elabree/hub75_esp32s3/Hardware_ZeDMD/ZeDMD_ESP32-S3/ZeDMD_ESP32-S3.kicad_sch

## KiCad design Hardware_ZeDMD/ZeDMD_ESP32-S3/ZeDMD_ESP32-S3.kicad_sch (2025-09-04)

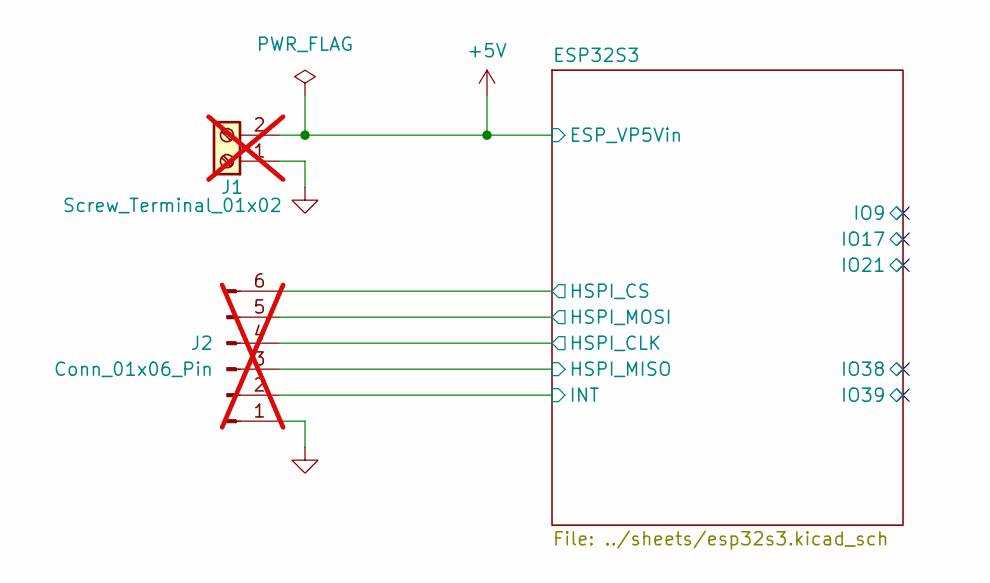
[picture p7: schematic ZeDMD_ESP32-S3.kicad_sch]

Parts:
J1: Screw_Terminal_01x02; TerminalBlock_Phoenix_MKDS-1,5-2-5.08_1x02_P5.08mm_Horizont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; not fitted
J2: Conn_01x06_Pin; PinHeader_1x06_P2.54mm_Vertical; not fitted

Connections:
+5V: J1.2
GND: J1.1, J2.1
HSPI_CLK: J2.4
HSPI_CS: J2.6
HSPI_MISO: J2.3
HSPI_MOSI: J2.5
INT: J2.2
