elabree/hub75_esp32s3/Hardware_ZeDMD/sheets/esp32s3.kicad_sch

## KiCad design Hardware_ZeDMD/sheets/esp32s3.kicad_sch (2025-09-04)

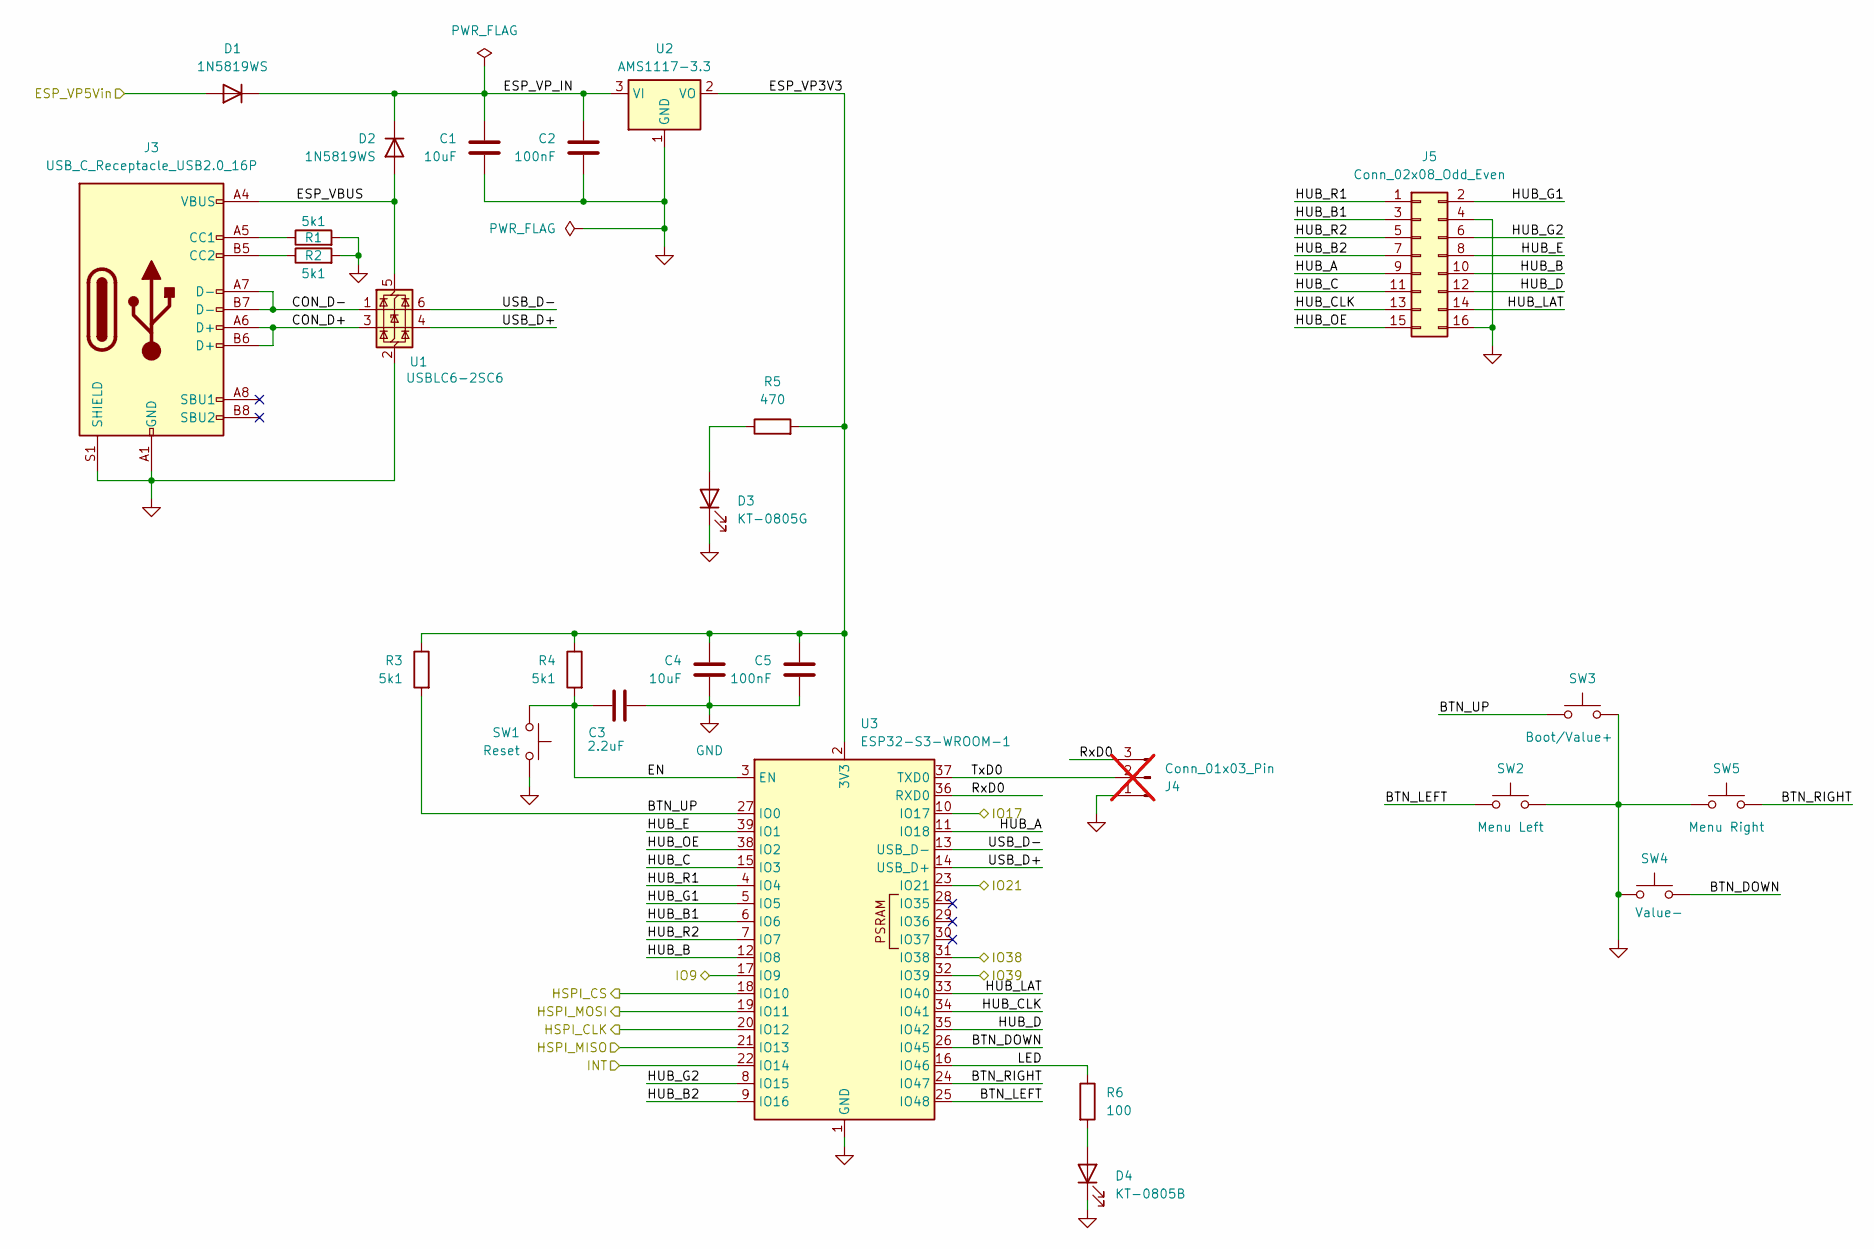
[picture p8: schematic esp32s3.kicad_sch]

Parts:
C1, C4: 10uF; C_0805_2012Metric; LCSC C15850
C2, C5: 100nF; C_0402_1005Metric; LCSC C1525
C3: 2.2uF; C_0603_1608Metric; LCSC C23630
D1, D2: 1N5819WS; D_SOD-323; LCSC C191023
D3: KT-0805G; LED_0805_2012Metric; LCSC C2297
D4: KT-0805B; LED_0805_2012Metric; LCSC C2293
J3: USB_C_Receptacle_USB2.0_16P; USB_C_Receptacle_XKB_U262-16XN-4BVC11; LCSC C709357
J4: Conn_01x03_Pin; PinHeader_1x03_P2.54mm_Vertical; not fitted
J5: Conn_02x08_Odd_Even; IDC-Header_2x08_P2.54mm_Vertical_SMD; LCSC C601969
R1, R2, R3, R4: 5k1; R_0603_1608Metric; LCSC C23186
R5: 470; R_0603_1608Metric; LCSC C23179
R6: 100; R_0603_1608Metric; LCSC C22775
SW1: Reset; SW_SPST_SKQG_WithStem; LCSC C318884
SW2: Menu Left; SW_SPST_SKQG_WithStem; LCSC C318884
SW3: Boot/Value+; SW_SPST_SKQG_WithStem; LCSC C318884
SW4: Value-; SW_SPST_SKQG_WithStem; LCSC C318884
SW5: Menu Right; SW_SPST_SKQG_WithStem; LCSC C318884
U1: USBLC6-2SC6; SOT-23-6; LCSC C7519
U2: AMS1117-3.3; SOT-223-3_TabPin2; LCSC C5346136
U3: ESP32-S3-WROOM-1; LCSC C2913202

Connections:
BTN_DOWN: SW4.1, U3.26 (IO45)
BTN_LEFT: SW2.1, U3.25 (IO48)
BTN_RIGHT: SW5.1, U3.24 (IO47)
BTN_UP: R3.2, SW3.1, U3.27 (IO0)
CON_D+: J3.A6 (D+), J3.B6 (D+), U1.3 (I/O2)
CON_D-: J3.A7 (D-), J3.B7 (D-), U1.1 (I/O1)
EN: C3.2, R4.2, SW1.2, U3.3 (EN)
ESP_VBUS: D2.2 (A), J3.A4 (VBUS), J3.A9 (VBUS), J3.B4 (VBUS), J3.B9 (VBUS), U1.5 (VBUS)
ESP_VP3V3: C4.1, C5.1, R3.1, R4.1, R5.2, U2.2 (VO), U3.2 (3V3)
ESP_VP5Vin: D1.2 (A)
ESP_VP_IN: C1.1, C2.1, D1.1 (K), D2.1 (K), U2.3 (VI)
GND: C1.2, C2.2, C3.1, C4.2, C5.2, D3.1 (K), D4.1 (K), J3.A1 (GND), J3.A12 (GND), J3.B1 (GND), J3.B12 (GND), J3.S1 (SHIELD), J4.1, J5.4, J5.16, R1.2, R2.2, SW1.1, SW2.2, SW3.2, SW4.2, SW5.2, U1.2 (GND), U2.1 (GND), U3.1 (GND), U3.40 (GND), U3.41 (GND)
HSPI_CLK: U3.20 (IO12)
HSPI_CS: U3.18 (IO10)
HSPI_MISO: U3.21 (IO13)
HSPI_MOSI: U3.19 (IO11)
HUB_A: J5.9, U3.11 (IO18)
HUB_B: J5.10, U3.12 (IO8)
HUB_B1: J5.3, U3.6 (IO6)
HUB_B2: J5.7, U3.9 (IO16)
HUB_C: J5.11, U3.15 (IO3)
HUB_CLK: J5.13, U3.34 (IO41)
HUB_D: J5.12, U3.35 (IO42)
HUB_E: J5.8, U3.39 (IO1)
HUB_G1: J5.2, U3.5 (IO5)
HUB_G2: J5.6, U3.8 (IO15)
HUB_LAT: J5.14, U3.33 (IO40)
HUB_OE: J5.15, U3.38 (IO2)
HUB_R1: J5.1, U3.4 (IO4)
HUB_R2: J5.5, U3.7 (IO7)
INT: U3.22 (IO14)
IO9: U3.17 (IO9)
IO17: U3.10 (IO17)
IO21: U3.23 (IO21)
IO38: U3.31 (IO38)
IO39: U3.32 (IO39)
LED: R6.1, U3.16 (IO46)
unnamed: D3.2 (A), R5.1
unnamed: D4.2 (A), R6.2
unnamed: J3.A5 (CC1), R1.1
unnamed: J3.B5 (CC2), R2.1
RxD0: J4.3, U3.36 (RXD0)
TxD0: J4.2, U3.37 (TXD0)
USB_D+: U1.4 (I/O2), U3.14 (USB_D+)
USB_D-: U1.6 (I/O1), U3.13 (USB_D-)
